promesoft/KicadJE-MidiToCV-MK2/Arduino/AJ_LFO_dual_out_CV1G1_CV2G1/wavetable.h

//const PROGMEM char SinTable[]=
//uint8_t waveTable[4][256] ={{0,3,6,9,12,15,18,21,24,27,30,33,36,39,42,45, 
uint8_t waveTable[256] ={127,124,121,118,115,112,109,106,103,100,97,94,91,88,85,82,
                            80,76,73,70,68,65,62,60,57,54,52,49,47,45,42,40,
                            38,36,33,31,29,27,25,24,22,20,19,17,15,14,13,11,
                            10,9,8,7,6,5,4,4,3,2,2,1,1,1,1,1,
                            0,1,1,1,1,1,2,2,3,4,4,5,6,7,8,9,
                            10,11,13,14,15,17,19,20,22,24,25,27,29,31,33,36,
                            38,40,42,45,47,49,52,54,57,60,62,65,68,70,73,76,
                            80,82,85,88,91,94,97,100,103,106,109,112,115,118,121,124,
                            127,130,133,136,139,142,145,148,151,154,157,160,163,166,169,172,
                            175,178,181,184,186,189,192,194,197,200,202,205,207,209,212,214,
                            216,218,221,223,225,227,229,230,232,234,235,237,239,240,241,243,
                            244,245,246,247,248,249,250,250,251,252,252,253,253,253,253,253,
                            254,253,253,253,253,253,252,252,251,250,250,249,248,247,246,245,
                            244,243,241,240,239,237,235,234,232,230,229,227,225,223,221,218,
                            216,214,212,209,207,205,202,200,197,194,192,189,186,184,181,178,
                            175,172,169,166,163,160,157,154,151,148,145,142,139,136,133,130,};

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
  183,  //18
  179,  //19
  175,  //20
  170,  //21
  166,  //22
  161,  //23
  157,  //24
  153,  //25
  148,  //26
  144,  //27
  139,  //28
  134,  //29
  130,  //30
  125,  //31
  121,  //32
  116,  //33
  112,  //34
  109,  //35
  105,  //36
  102,  //37
  99, //38
  96, //39
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

};*/
